bokumentation/STASRG-SulfurMonitoring-Hardware/firmware/data_logger_heltec_arduino/main/sensor/tb600_sensor.h

// tb600_sensor.h
#pragma once

#include "esp_err.h"
#include "hal/uart_types.h"
#include "tb600_sensor_cmd.h"

/**
 * @brief Structure to hold the combined sensor data.
 */
typedef struct {
    float temperature_c; // Temperature in Celsius
    float humidity_perc; // Humidity in percentage
    float gas_ugm3;      // Gas concentration in ug/m³
    bool success;
} tb600b_combined_data_t;

// --- MOLECULAR WEIGHTS (g/mol) for accurate conversions ---
// These values are standard for STP conversions.
#define M_W_SO2 64.06f // Sulfur Dioxide
#define M_W_H2S 34.08f // Hydrogen Sulfide

static const int RX_BUF_SIZE = 128;

#define TB600B_RESPONSE_HEADER_BYTE1 0xFF
#define TB600B_RESPONSE_HEADER_BYTE2 0x87
#define TB600B_RESPONSE_LENGTH       13
#define TB600_TAG_UART_SENSOR        "TB600_LIBS"

/**
 * @brief Inisialisasi UART untuk sensor TB600B/C.
 * @param uart_num The UART port number to use (e.g., UART_NUM_1).
 * @param tx_pin GPIO yang digunakan untuk transmisi (TX).
 * @param rx_pin GPIO yang digunakan untuk penerimaan (RX).
 * @param tag TAG untuk logging dan debugging.
 * @return void
 */
void tb600b_init_uart(uart_port_t uart_num, int tx_pin, int rx_pin, const char *tag);

/**
 * @brief Membaca data dari sensor TB600.
 * @param uart_num The UART port number to use (e.g., UART_NUM_1).
 * @param command Perintah byte array yang akan dikirim ke sensor.
 * @param commandSize Ukuran dari array perintah.
 * @param data_out Pointer ke struktur tb600b_combined_data_t untuk menyimpan data yang dibaca.
 * @note Fungsi ini mengirim perintah ke sensor, menunggu respons, dan mengurai data yang diterima.
 *       Pastikan untuk memanggil fungsi ini dalam konteks task FreeRTOS yang sesuai,
 *       karena fungsi ini dapat memblokir hingga data diterima.
 * @note Fungsi ini mengharapkan respons dalam format yang telah ditentukan oleh protokol TB600B/C.
 *       Respons harus dimulai dengan header byte yang benar (0xFF, 0x87)
 *       dan diakhiri dengan checksum yang valid.
 * @return void
 */
esp_err_t tb600b_read_combined_data(uart_port_t uart_num, const uint8_t *command, size_t commandSize, tb600b_combined_data_t *data_out);

/**
 * @brief Sends command, reads and parses sensor data, returning the data struct directly.
 * This is the preferred, safe, high-level access function.
 * * @param uart_num The UART port number.
 * @param command The command byte array to send to the sensor.
 * @param commandSize Size of the command array.
 * @return tb600b_combined_data_t A structure containing sensor data and a success flag.
 */
tb600b_combined_data_t tb600b_get_data_safe(uart_port_t uart_num, const uint8_t *command, size_t commandSize);

/**
 * @brief Converts gas concentration from micrograms per cubic meter (ug/m³) to parts per million (ppm),
 * correcting for the ambient temperature.
 * * @param ugm3_concentration Concentration in ug/m³.
 * @param temperature_c Ambient temperature in Celsius (T in the Ideal Gas Law).
 * @param molecular_weight Molecular weight of the gas in g/mol (M).
 * @return float The concentration in ppm.
 */
float tb600b_convert_ugm3_to_ppm(float ugm3_concentration, float temperature_c, float molecular_weight);

void tb600b_read_confirmation();
void tb600b_read_status_response();
void tb600b_set_passive_mode(uart_port_t uart_num, const char *tag);

// Define
#define TB600_TAG_LED "TB600_LED"

// LED COMMANDs
void led_read_confirmation(uart_port_t uart_num, const char *tag);
void led_read_status_response(uart_port_t uart_num, const char *tag);
void led_get_led_status(uart_port_t uart_num, const char *tag);
void led_turn_off_led(uart_port_t uart_num, const char *tag);
void led_turn_on_led(uart_port_t uart_num, const char *tag);
void led_set_passive_mode(uart_port_t uart_num, const char *tag);
