bokumentation/STASRG-SulfurMonitoring-Hardware/firmware/data_logger_heltec_arduino/main/sensor/tb600_sensor_cmd.h

// tb600_sensor_cmd.h
#pragma once
#include <cstdint>

/* --- SO2 GAS SENSOR TYPE: 0x24--- */
// ✅ Cmd 6: to get combined gas concentration, temperature, and humidity:
// [2]=0x87 Return: 13 bytes
static const uint8_t CMD_GET_COMBINED_DATA[] = {0xFF, 0x01, 0x87, 0x00, 0x00, 0x00, 0x00, 0x00, 0x78};

// ✅ Command to CHECK LED status
// Return: 0 or 1
static const uint8_t CMD_GET_LED_STATUS[] = {0xFF, 0x01, 0x8A, 0x00, 0x00, 0x00, 0x00, 0x00, 0x75};

// ✅ Command to turn OFF LED
// Return: OK
static const uint8_t CMD_TURN_OFF_LED[] = {0xFF, 0x01, 0x88, 0x00, 0x00, 0x00, 0x00, 0x00, 0x77};

// ✅ Command to turn ON LED
// Return: OK
static const uint8_t CMD_TURN_ON_LED[] = {0xFF, 0x01, 0x89, 0x00, 0x00, 0x00, 0x00, 0x00, 0x76};

// ✅ Command 2: Switches to PASSIVE UPLOAD (sensor waits for commands)
// Return: ❌
static const uint8_t CMDSET_MODE_PASSIVE_UPLOAD[] = {0xFF, 0x01, 0x78, 0x41, 0x00, 0x00, 0x00, 0x00, 0x46};
