bokumentation/STASRG-SulfurMonitoring-Hardware/firmware/test/i2c_bus_scanner/main/main.c

#include <freertos/FreeRTOS.h>
#include <freertos/task.h>
#include <i2cdev.h>
#include <stdio.h>
#include "board_pins.h"

void task(void *ignore)
{
    i2c_dev_t dev = { 0 };
    dev.cfg.sda_io_num = PIN_I2C_SDA;
    dev.cfg.scl_io_num = PIN_I2C_SCL;
#if HELPER_TARGET_IS_ESP32
    dev.cfg.master.clk_speed = I2C_MASTER_FREQ_HZ; // 100kHz
#endif
    while (1)
    {
        esp_err_t res;
        printf("     0  1  2  3  4  5  6  7  8  9  a  b  c  d  e  f\n");
        printf("00:         ");
        for (uint8_t addr = 3; addr < 0x78; addr++)
        {
            if (addr % 16 == 0)
                printf("\n%.2x:", addr);

            dev.addr = addr;
            res = i2c_dev_probe(&dev, I2C_DEV_WRITE);

            if (res == 0)
                printf(" %.2x", addr);
            else
                printf(" --");
        }
        printf("\n\n");
        vTaskDelay(pdMS_TO_TICKS(1000));
    }
}

void app_main()
{
    // Init i2cdev library
    ESP_ERROR_CHECK(i2cdev_init());
    // Start task
    xTaskCreate(task, "i2c_scanner", configMINIMAL_STACK_SIZE * 3, NULL, 5, NULL);
}
