bokumentation/STASRG-SulfurMonitoring-Hardware/firmware/test/ina219_test/main/main.c

#include <stdio.h>
#include <freertos/FreeRTOS.h>
#include <freertos/task.h>
#include <ina219.h>
#include <string.h>
#include <esp_log.h>
#include <assert.h>
#include "board_pins.h"

#define I2C_PORT I2C_MASTER_NUM
#define I2C_ADDR I2C_HW_ADDR_SENSOR_INA219_1
#define CONFIG_EXAMPLE_SHUNT_RESISTOR_MILLI_OHM 100
#define CONFIG_EXAMPLE_I2C_MASTER_SDA PIN_I2C_SDA
#define CONFIG_EXAMPLE_I2C_MASTER_SCL PIN_I2C_SCL

const static char *TAG = "INA219_example";

void task(void *pvParameters)
{
    ina219_t dev;
    memset(&dev, 0, sizeof(ina219_t));

    assert(CONFIG_EXAMPLE_SHUNT_RESISTOR_MILLI_OHM > 0);
    ESP_ERROR_CHECK(ina219_init_desc(&dev, I2C_ADDR, I2C_PORT, CONFIG_EXAMPLE_I2C_MASTER_SDA, CONFIG_EXAMPLE_I2C_MASTER_SCL));
   
    ESP_LOGI(TAG, "Initializing INA219");
    ESP_ERROR_CHECK(ina219_init(&dev));

    ESP_LOGI(TAG, "Configuring INA219");
    ESP_ERROR_CHECK(ina219_configure(&dev, INA219_BUS_RANGE_16V, INA219_GAIN_0_125,
                                     INA219_RES_12BIT_1S, INA219_RES_12BIT_1S, INA219_MODE_CONT_SHUNT_BUS));

    ESP_LOGI(TAG, "Calibrating INA219");

    ESP_ERROR_CHECK(ina219_calibrate(&dev, (float)CONFIG_EXAMPLE_SHUNT_RESISTOR_MILLI_OHM / 1000.0f));

    float bus_voltage, shunt_voltage, current, power;

    ESP_LOGI(TAG, "Starting the loop");
    while (1)
    {
        ESP_ERROR_CHECK(ina219_get_bus_voltage(&dev, &bus_voltage));
        ESP_ERROR_CHECK(ina219_get_shunt_voltage(&dev, &shunt_voltage));
        ESP_ERROR_CHECK(ina219_get_current(&dev, &current));
        ESP_ERROR_CHECK(ina219_get_power(&dev, &power));
        /* Using float in printf() requires non-default configuration in
         * sdkconfig. See sdkconfig.defaults.esp32 and
         * sdkconfig.defaults.esp8266  */
        printf("VBUS: %.04f V, VSHUNT: %.04f mV, IBUS: %.04f mA, PBUS: %.04f mW\n",
               bus_voltage, shunt_voltage * 1000, current * 1000, power * 1000);

        vTaskDelay(pdMS_TO_TICKS(500));
    }
}

void app_main()
{
    ESP_ERROR_CHECK(i2cdev_init());
    xTaskCreate(task, "test", configMINIMAL_STACK_SIZE * 8, NULL, 5, NULL);
}
