bokumentation/STASRG-SulfurMonitoring-Hardware/firmware/test/sd_card_arduino/components/espsoftwareserial/SoftwareSerial.h

/*
SoftwareSerial.h - Implementation of the Arduino software serial for ESP8266/ESP32.
Copyright (c) 2015-2016 Peter Lerup. All rights reserved.
Copyright (c) 2018-2019 Dirk O. Kaar. All rights reserved.

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
You should have received a copy of the GNU Lesser General Public
License along with this library; if not, write to the Free Software
Foundation, Inc., 51 Franklin St, Fifth Floor, Boston, MA  02110-1301  USA
*/

#ifndef __SoftwareSerial_h
#define __SoftwareSerial_h

#include <circular_queue.h>
#include <Stream.h>

// Define lets bittiming calculation be based on cpu cycles instead
// microseconds. This has higher resolution and general precision under
// low-load conditions, but whenever the CPU frequency gets switched,
// like during WiFi operation, it in turn is much more imprecise.
// TODO: increase average timing precision in CCY mode by computing
// bit durations in 10ths of micros.
#undef CCY_TICKS

namespace EspSoftwareSerial {

// Interface definition for template argument of BasicUART
class IGpioCapabilities {
public:
    static constexpr bool isValidPin(int8_t pin);
    static constexpr bool isValidInputPin(int8_t pin);
    static constexpr bool isValidOutputPin(int8_t pin);
    // result is only defined for a valid Rx pin
    static constexpr bool hasPullUp(int8_t pin);
};

class GpioCapabilities : private IGpioCapabilities {
public:
    static constexpr bool isValidPin(int8_t pin) {
    #if defined(ESP8266)
        return (pin >= 0 && pin <= 16) && !isFlashInterfacePin(pin);
    #elif defined(ESP32)
        // Remove the strapping pins as defined in the datasheets, they affect bootup and other critical operations
        // Remove the flash memory pins on related devices, since using these causes memory access issues.
    #ifdef CONFIG_IDF_TARGET_ESP32
        // Datasheet https://www.espressif.com/sites/default/files/documentation/esp32_datasheet_en.pdf,
        // Pinout    https://docs.espressif.com/projects/esp-idf/en/latest/esp32/_images/esp32-devkitC-v4-pinout.jpg
        return (pin == 1) || (pin >= 3 && pin <= 5) ||
            (pin >= 12 && pin <= 15) ||
            (!psramFound() && pin >= 16 && pin <= 17) ||
            (pin >= 18 && pin <= 19) ||
            (pin >= 21 && pin <= 23) || (pin >= 25 && pin <= 27) || (pin >= 32 && pin <= 39);
    #elif CONFIG_IDF_TARGET_ESP32S2
        // Datasheet https://www.espressif.com/sites/default/files/documentation/esp32-s2_datasheet_en.pdf,
        // Pinout    https://docs.espressif.com/projects/esp-idf/en/latest/esp32s2/_images/esp32-s2_saola1-pinout.jpg
        return (pin >= 1 && pin <= 21) || (pin >= 33 && pin <= 44);
    #elif CONFIG_IDF_TARGET_ESP32C3
        // Datasheet https://www.espressif.com/sites/default/files/documentation/esp32-c3_datasheet_en.pdf,
        // Pinout    https://docs.espressif.com/projects/esp-idf/en/latest/esp32c3/_images/esp32-c3-devkitm-1-v1-pinout.jpg
        return (pin >= 0 && pin <= 1) || (pin >= 3 && pin <= 7) || (pin >= 18 && pin <= 21);
    #else
        return pin >= 0;
    #endif
    #else
        return pin >= 0;
    #endif
    }

    static constexpr bool isValidInputPin(int8_t pin) {
        return isValidPin(pin)
    #if defined(ESP8266)
            && (pin != 16)
    #endif
            ;
    }

    static constexpr bool isValidOutputPin(int8_t pin) {
        return isValidPin(pin)
    #if defined(ESP32)
    #ifdef CONFIG_IDF_TARGET_ESP32
            && (pin < 34)
    #elif CONFIG_IDF_TARGET_ESP32S2
            && (pin <= 45)
    #elif CONFIG_IDF_TARGET_ESP32C3
            // no restrictions
    #endif
    #endif
            ;
    }

    // result is only defined for a valid Rx pin
    static constexpr bool hasPullUp(int8_t pin) {
    #if defined(ESP32)
        return !(pin >= 34 && pin <= 39);
    #else
        (void)pin;
        return true;
    #endif
    }
};

enum Parity : uint8_t {
    PARITY_NONE = 000,
    PARITY_EVEN = 020,
    PARITY_ODD = 030,
    PARITY_MARK = 040,
    PARITY_SPACE = 070,
};

enum Config {
    SWSERIAL_5N1 = PARITY_NONE,
    SWSERIAL_6N1,
    SWSERIAL_7N1,
    SWSERIAL_8N1,
    SWSERIAL_5E1 = PARITY_EVEN,
    SWSERIAL_6E1,
    SWSERIAL_7E1,
    SWSERIAL_8E1,
    SWSERIAL_5O1 = PARITY_ODD,
    SWSERIAL_6O1,
    SWSERIAL_7O1,
    SWSERIAL_8O1,
    SWSERIAL_5M1 = PARITY_MARK,
    SWSERIAL_6M1,
    SWSERIAL_7M1,
    SWSERIAL_8M1,
    SWSERIAL_5S1 = PARITY_SPACE,
    SWSERIAL_6S1,
    SWSERIAL_7S1,
    SWSERIAL_8S1,
    SWSERIAL_5N2 = 0200 | PARITY_NONE,
    SWSERIAL_6N2,
    SWSERIAL_7N2,
    SWSERIAL_8N2,
    SWSERIAL_5E2 = 0200 | PARITY_EVEN,
    SWSERIAL_6E2,
    SWSERIAL_7E2,
    SWSERIAL_8E2,
    SWSERIAL_5O2 = 0200 | PARITY_ODD,
    SWSERIAL_6O2,
    SWSERIAL_7O2,
    SWSERIAL_8O2,
    SWSERIAL_5M2 = 0200 | PARITY_MARK,
    SWSERIAL_6M2,
    SWSERIAL_7M2,
    SWSERIAL_8M2,
    SWSERIAL_5S2 = 0200 | PARITY_SPACE,
    SWSERIAL_6S2,
    SWSERIAL_7S2,
    SWSERIAL_8S2,
};

/// This class is compatible with the corresponding AVR one, however,
/// the constructor takes no arguments, for compatibility with the
/// HardwareSerial class.
/// Instead, the begin() function handles pin assignments and logic inversion.
/// It also has optional input buffer capacity arguments for byte buffer and ISR bit buffer.
/// Bitrates up to at least 115200 can be used.
class UARTBase : public Stream {
public:
    UARTBase();
    /// Ctor to set defaults for pins.
    /// @param rxPin the GPIO pin used for RX
    /// @param txPin -1 for onewire protocol, GPIO pin used for twowire TX
    UARTBase(int8_t rxPin, int8_t txPin = -1, bool invert = false);
    UARTBase(const UARTBase&) = delete;
    UARTBase& operator= (const UARTBase&) = delete;
    virtual ~UARTBase();
    /// Configure the UARTBase object for use.
    /// @param baud the TX/RX bitrate
    /// @param config sets databits, parity, and stop bit count
    /// @param rxPin -1 or default: either no RX pin, or keeps the rxPin set in the ctor
    /// @param txPin -1 or default: either no TX pin (onewire), or keeps the txPin set in the ctor
    /// @param invert true: uses invert line level logic
    /// @param bufCapacity the capacity for the received bytes buffer
    /// @param isrBufCapacity 0: derived from bufCapacity. The capacity of the internal asynchronous
    ///        bit receive buffer, a suggested size is bufCapacity times the sum of
    ///        start, data, parity and stop bit count.
    void begin(uint32_t baud, Config config,
        int8_t rxPin, int8_t txPin, bool invert);

    uint32_t baudRate();
    /// Transmit control pin.
    void setTransmitEnablePin(int8_t txEnablePin);
    /// Enable (default) or disable interrupts during tx.
    void enableIntTx(bool on);
    /// Enable (default) or disable internal rx GPIO pull-up.
    void enableRxGPIOPullUp(bool on);
    /// Enable or disable (default) tx GPIO output mode.
    void enableTxGPIOOpenDrain(bool on);

    bool overflow();

    int available() override;
#if defined(ESP8266)
    int availableForWrite() override {
#else
    int availableForWrite() {
#endif
        if (!m_txValid) return 0;
        return 1;
    }
    int peek() override;
    int read() override;
    /// @returns The verbatim parity bit associated with the last successful read() or peek() call
    bool readParity()
    {
        return m_lastReadParity;
    }
    /// @returns The calculated bit for even parity of the parameter byte
    static bool parityEven(uint8_t byte) {
        byte ^= byte >> 4;
        byte &= 0xf;
        return (0x6996 >> byte) & 1;
    }
    /// @returns The calculated bit for odd parity of the parameter byte
    static bool parityOdd(uint8_t byte) {
        byte ^= byte >> 4;
        byte &= 0xf;
        return (0x9669 >> byte) & 1;
    }
    /// The read(buffer, size) functions are non-blocking, the same as readBytes but without timeout
    int read(uint8_t* buffer, size_t size)
#if defined(ESP8266)
        override
#endif
        ;
    /// The read(buffer, size) functions are non-blocking, the same as readBytes but without timeout
    int read(char* buffer, size_t size) {
        return read(reinterpret_cast<uint8_t*>(buffer), size);
    }
    /// @returns The number of bytes read into buffer, up to size. Times out if the limit set through
    ///          Stream::setTimeout() is reached.
    size_t readBytes(uint8_t* buffer, size_t size) override;
    /// @returns The number of bytes read into buffer, up to size. Times out if the limit set through
    ///          Stream::setTimeout() is reached.
    size_t readBytes(char* buffer, size_t size) override {
        return readBytes(reinterpret_cast<uint8_t*>(buffer), size);
    }
    void flush() override;
    size_t write(uint8_t byte) override;
    size_t write(uint8_t byte, Parity parity);
    size_t write(const uint8_t* buffer, size_t size) override;
    size_t write(const char* buffer, size_t size) {
        return write(reinterpret_cast<const uint8_t*>(buffer), size);
    }
    size_t write(const uint8_t* buffer, size_t size, Parity parity);
    size_t write(const char* buffer, size_t size, Parity parity) {
        return write(reinterpret_cast<const uint8_t*>(buffer), size, parity);
    }
    operator bool() const {
        return (-1 == m_rxPin || m_rxValid) && (-1 == m_txPin || m_txValid) && !(-1 == m_rxPin && m_oneWire);
    }

    /// Disable or enable interrupts on the rx pin.
    void enableRx(bool on);
    /// One wire control.
    void enableTx(bool on);

    // AVR compatibility methods.
    bool listen() { enableRx(true); return true; }
    void end();
    bool isListening() { return m_rxEnabled; }
    bool stopListening() { enableRx(false); return true; }

    /// onReceive sets a callback that will be called in interrupt context
    /// when data is received.
    /// More precisely, the callback is triggered when UARTBase detects
    /// a new reception, which may not yet have completed on invocation.
    /// Reading - never from this interrupt context - should therefore be
    /// delayed at least for the duration of one incoming word.
    void onReceive(const Delegate<void(), void*>& handler);
    /// onReceive sets a callback that will be called in interrupt context
    /// when data is received.
    /// More precisely, the callback is triggered when UARTBase detects
    /// a new reception, which may not yet have completed on invocation.
    /// Reading - never from this interrupt context - should therefore be
    /// delayed at least for the duration of one incoming word.
    void onReceive(Delegate<void(), void*>&& handler);

    [[deprecated("function removed; semantics of onReceive() changed; check the header file.")]]
    void perform_work();

    using Print::write;

protected:
    void beginRx(bool hasPullUp, int bufCapacity, int isrBufCapacity);
    void beginTx();
    // Member variables
    int8_t m_rxPin = -1;
    int8_t m_txPin = -1;
    bool m_invert = false;

private:
    // It's legal to exceed the deadline, for instance,
    // by enabling interrupts.
    void lazyDelay();
    // Synchronous precise delay
    void preciseDelay();
    // If withStopBit is set, either cycle contains a stop bit.
    // If dutyCycle == 0, the level is not forced to HIGH.
    // If offCycle == 0, the level remains unchanged from dutyCycle.
    void writePeriod(
        uint32_t dutyCycle, uint32_t offCycle, bool withStopBit);
    // safely set the pin mode for the Rx GPIO pin
    void setRxGPIOPinMode();
    // safely set the pin mode for the Tx GPIO pin
    void setTxGPIOPinMode();
    /* check m_rxValid that calling is safe */
    void rxBits();
    void rxBits(const uint32_t isrTick);
    static void disableInterrupts();
    static void restoreInterrupts();

    static void rxBitISR(UARTBase* self);
    static void rxBitSyncISR(UARTBase* self);

    static inline uint32_t IRAM_ATTR ticks() ALWAYS_INLINE_ATTR {
#ifdef CCYTICKS
        return ESP.getCycleCount() << 1;
#else
        return micros() << 1;
#endif // CCYTICKS
    }
    static inline uint32_t IRAM_ATTR microsToTicks(uint32_t micros) ALWAYS_INLINE_ATTR {
#ifdef CCYTICKS
        return (ESP.getCpuFreqMHz() * micros) << 1;
#else
        return micros << 1;
#endif // CCYTICKS
    }
    static inline uint32_t ticksToMicros(uint32_t ticks) ALWAYS_INLINE_ATTR {
#ifdef CCYTICKS
        return (ticks >> 1) / ESP.getCpuFreqMHz();
#else
        return ticks >> 1;
#endif // CCYTICKS
    }

    // Member variables
    volatile uint32_t* m_rxReg;
    uint32_t m_rxBitMask;
#if !defined(ESP8266)
    volatile uint32_t* m_txReg;
#endif
    uint32_t m_txBitMask;
    int8_t m_txEnablePin = -1;
    uint8_t m_dataBits;
    bool m_oneWire;
    bool m_rxValid = false;
    bool m_rxEnabled = false;
    bool m_txValid = false;
    bool m_txEnableValid = false;
    /// PDU bits include data, parity and stop bits; the start bit is not counted.
    uint8_t m_pduBits;
    bool m_intTxEnabled;
    bool m_rxGPIOHasPullUp = false;
    bool m_rxGPIOPullUpEnabled = true;
    bool m_txGPIOOpenDrain = false;
    Parity m_parityMode;
    uint8_t m_stopBits;
    bool m_lastReadParity;
    bool m_overflow = false;
    uint32_t m_bitTicks;
    uint8_t m_parityInPos;
    uint8_t m_parityOutPos;
    int8_t m_rxLastBit; // 0 thru (m_pduBits - m_stopBits - 1): data/parity bits. -1: start bit. (m_pduBits - 1): stop bit.
    uint8_t m_rxCurByte = 0;
    std::unique_ptr<circular_queue<uint8_t> > m_buffer;
    std::unique_ptr<circular_queue<uint8_t> > m_parityBuffer;
    uint32_t m_periodStart;
    uint32_t m_periodDuration;
#ifndef ESP32
    static uint32_t m_savedPS;
#else
    static portMUX_TYPE m_interruptsMux;
#endif
    // the ISR stores the relative bit times in the buffer. The inversion corrected level is used as sign bit (2's complement):
    // 1 = positive including 0, 0 = negative.
    std::unique_ptr<circular_queue<uint32_t, UARTBase*> > m_isrBuffer;
    const Delegate<void(uint32_t&&), UARTBase*> m_isrBufferForEachDel { [](UARTBase* self, uint32_t&& isrTick) { self->rxBits(isrTick); }, this };
    std::atomic<bool> m_isrOverflow { false };
    uint32_t m_isrLastTick;
    bool m_rxCurParity = false;
    Delegate<void(), void*> m_rxHandler;
};

template< class GpioCapabilities > class BasicUART : public UARTBase {
    static_assert(std::is_base_of<IGpioCapabilities, GpioCapabilities>::value,
        "template argument is not derived from IGpioCapabilities");
public:
    BasicUART() : UARTBase() {
    }
    /// Ctor to set defaults for pins.
    /// @param rxPin the GPIO pin used for RX
    /// @param txPin -1 for onewire protocol, GPIO pin used for twowire TX
    BasicUART(int8_t rxPin, int8_t txPin = -1, bool invert = false) :
        UARTBase(rxPin, txPin, invert) {
    }

    /// Configure the BasicUART object for use.
    /// @param baud the TX/RX bitrate
    /// @param config sets databits, parity, and stop bit count
    /// @param rxPin -1 or default: either no RX pin, or keeps the rxPin set in the ctor
    /// @param txPin -1 or default: either no TX pin (onewire), or keeps the txPin set in the ctor
    /// @param invert true: uses invert line level logic
    /// @param bufCapacity the capacity for the received bytes buffer
    /// @param isrBufCapacity 0: derived from bufCapacity. The capacity of the internal asynchronous
    ///        bit receive buffer, a suggested size is bufCapacity times the sum of
    ///        start, data, parity and stop bit count.
    void begin(uint32_t baud, Config config,
        int8_t rxPin, int8_t txPin, bool invert,
        int bufCapacity = 64, int isrBufCapacity = 0) {
        UARTBase::begin(baud, config, rxPin, txPin, invert);
        if (GpioCapabilities::isValidInputPin(rxPin)) {
            beginRx(GpioCapabilities:: hasPullUp(rxPin), bufCapacity, isrBufCapacity);
        }
        if (GpioCapabilities::isValidOutputPin(txPin)) {
            beginTx();
        }
        enableRx(true);
    }
    void begin(uint32_t baud, Config config,
        int8_t rxPin, int8_t txPin) {
        begin(baud, config, rxPin, txPin, m_invert);
    }
    void begin(uint32_t baud, Config config,
        int8_t rxPin) {
        begin(baud, config, rxPin, m_txPin, m_invert);
    }
    void begin(uint32_t baud, Config config = SWSERIAL_8N1) {
        begin(baud, config, m_rxPin, m_txPin, m_invert);
    }
    void setTransmitEnablePin(int8_t txEnablePin) {
        UARTBase::setTransmitEnablePin(
            GpioCapabilities::isValidOutputPin(txEnablePin) ? txEnablePin : -1);
    }
};

using UART = BasicUART< GpioCapabilities >;

}; // namespace EspSoftwareSerial

using SoftwareSerial = EspSoftwareSerial::UART;
using SoftwareSerialParity = EspSoftwareSerial::Parity;
using SoftwareSerialConfig = EspSoftwareSerial::Config;
using EspSoftwareSerial::SWSERIAL_5N1;
using EspSoftwareSerial::SWSERIAL_6N1;
using EspSoftwareSerial::SWSERIAL_7N1;
using EspSoftwareSerial::SWSERIAL_8N1;
using EspSoftwareSerial::SWSERIAL_5E1;
using EspSoftwareSerial::SWSERIAL_6E1;
using EspSoftwareSerial::SWSERIAL_7E1;
using EspSoftwareSerial::SWSERIAL_8E1;
using EspSoftwareSerial::SWSERIAL_5O1;
using EspSoftwareSerial::SWSERIAL_6O1;
using EspSoftwareSerial::SWSERIAL_7O1;
using EspSoftwareSerial::SWSERIAL_8O1;
using EspSoftwareSerial::SWSERIAL_5M1;
using EspSoftwareSerial::SWSERIAL_6M1;
using EspSoftwareSerial::SWSERIAL_7M1;
using EspSoftwareSerial::SWSERIAL_8M1;
using EspSoftwareSerial::SWSERIAL_5S1;
using EspSoftwareSerial::SWSERIAL_6S1;
using EspSoftwareSerial::SWSERIAL_7S1;
using EspSoftwareSerial::SWSERIAL_8S1;
using EspSoftwareSerial::SWSERIAL_5N2;
using EspSoftwareSerial::SWSERIAL_6N2;
using EspSoftwareSerial::SWSERIAL_7N2;
using EspSoftwareSerial::SWSERIAL_8N2;
using EspSoftwareSerial::SWSERIAL_5E2;
using EspSoftwareSerial::SWSERIAL_6E2;
using EspSoftwareSerial::SWSERIAL_7E2;
using EspSoftwareSerial::SWSERIAL_8E2;
using EspSoftwareSerial::SWSERIAL_5O2;
using EspSoftwareSerial::SWSERIAL_6O2;
using EspSoftwareSerial::SWSERIAL_7O2;
using EspSoftwareSerial::SWSERIAL_8O2;
using EspSoftwareSerial::SWSERIAL_5M2;
using EspSoftwareSerial::SWSERIAL_6M2;
using EspSoftwareSerial::SWSERIAL_7M2;
using EspSoftwareSerial::SWSERIAL_8M2;
using EspSoftwareSerial::SWSERIAL_5S2;
using EspSoftwareSerial::SWSERIAL_6S2;
using EspSoftwareSerial::SWSERIAL_7S2;
using EspSoftwareSerial::SWSERIAL_8S2;

#if __GNUC__ < 12
// The template member functions below must be in IRAM, but due to a bug GCC doesn't currently
// honor the attribute. Instead, it is possible to do explicit specialization and adorn
// these with the IRAM attribute:
// Delegate<>::operator (), circular_queue<>::available,
// circular_queue<>::available_for_push, circular_queue<>::push_peek, circular_queue<>::push

extern template void delegate::detail::DelegateImpl<void*, void>::operator()() const;
extern template size_t circular_queue<uint32_t, EspSoftwareSerial::UARTBase*>::available() const;
extern template bool circular_queue<uint32_t, EspSoftwareSerial::UARTBase*>::push(uint32_t&&);
extern template bool circular_queue<uint32_t, EspSoftwareSerial::UARTBase*>::push(const uint32_t&);
#endif // __GNUC__ < 12

#endif // __SoftwareSerial_h
