bokumentation/STASRG-SulfurMonitoring-Hardware/firmware/data_logger_heltec_arduino/examples/rtc.cpp

#include "RTClib.h"
#include "Wire.h"
#include <Arduino.h>


RTC_DS1307 rtc;



void ujicoba_rtc()
{
 
    if (!rtc.begin()) {
        Serial.println("Couldn't find RTC");
        Serial.flush();
        while (1)
            delay(10);
    }

    if (!rtc.isrunning()) {
        Serial.println("RTC is NOT running, let's set the time!");
        rtc.adjust(DateTime(F(__DATE__), F(__TIME__)));
    }

    DateTime time = rtc.now();

    // Full Timestamp
    Serial.println(String("DateTime::TIMESTAMP_FULL:\t") + time.timestamp(DateTime::TIMESTAMP_FULL));

    // Date Only
    Serial.println(String("DateTime::TIMESTAMP_DATE:\t") + time.timestamp(DateTime::TIMESTAMP_DATE));

    // Full Timestamp
    Serial.println(String("DateTime::TIMESTAMP_TIME:\t") + time.timestamp(DateTime::TIMESTAMP_TIME));

    Serial.println("\n");

    // Delay 5s
    delay(5000);
}
